Avikmen/USB-RF-Gateway/Images/IMG_20190824_114829-01.jpeg

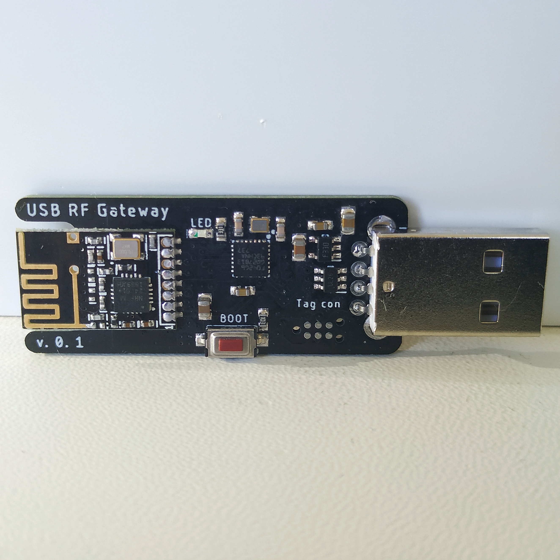
Images/IMG_20190824_114829-01.jpeg
