Avikmen/USB-RF-Gateway/Images/IMG_20190824_114843-01.jpeg

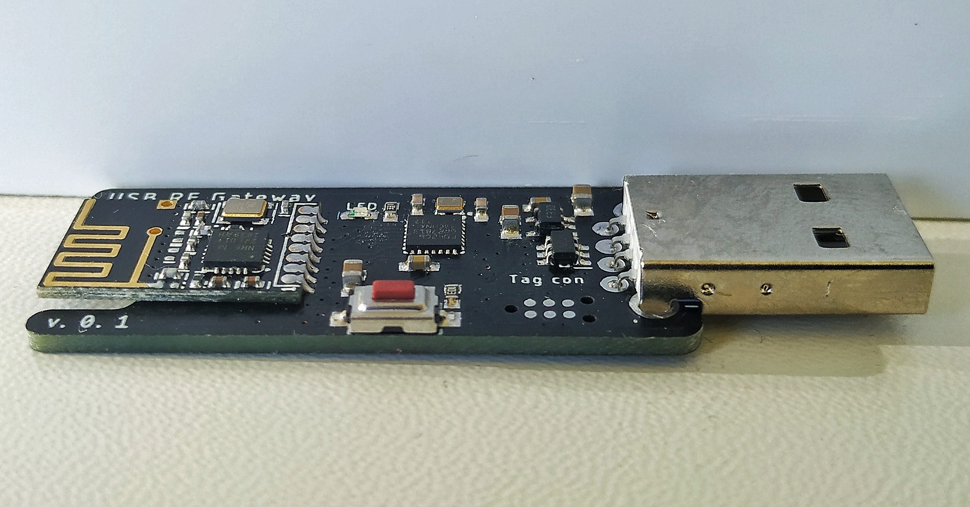
Images/IMG_20190824_114843-01.jpeg
